ksevelyar/habits-stepper/case/mixin.scad

wall = 2;
overcut = 0.1;
battery_slot_diameter = 32.5;
diameter = 72;
display_length = 77;
display_pcb_width = 19.2;
display_slot_width = 21;
display_slot_length = 67;
display_window_length = 56;
display_window_width = 17.4;
esp32c3_width = 18.5;
esp32c3_length = 24;
tp4057_width = 14.5;
tp4057_length = 14;

module rail_side(half_width, length, y, rail_height = 9) {
  translate([-half_width - 2, y, 2]) cube([2, length, rail_height]);
  hull() {
    translate([-half_width - 0.15, y, 2 + rail_height - 3.5]) rotate([0, -40, 0]) cube([1.5, length, 1]);
    translate([-half_width - 0.5, y, 2 + rail_height - 2.6]) cube([1.5, length, 1]);
  }
  translate([-half_width - 0.35, y, 2 + rail_height - 1.0]) rotate([0, -40, 0]) cube([1.3, length, 1]);
}

module rail(half_width, length, y, rail_height = 9) {
  rail_side(half_width, length, y, rail_height);
  mirror([1, 0, 0]) rail_side(half_width, length, y, rail_height);
}

module esp32c3_mini_rails() {
  rail(esp32c3_width / 2, esp32c3_length - 8, 19);
}

module tp4057_rails() {
  rail(tp4057_width / 2, tp4057_length, -36, 13);
}

module button_cutout() {
  size = 14.1;
  translate([-size / 2, -24.5, -2.5]) cube(size=size);
}

module display_slot_cutout() {
  translate([-display_slot_length / 2, (display_pcb_width - display_slot_width) / 2, 0.4]) cube([display_slot_length, display_slot_width, 100]);
}

module display_window_cutout(clearance = 0) {
  width = display_window_width + clearance;
  translate([-display_window_length / 2, (display_pcb_width - width) / 2, -0.1])
    cube([display_window_length, width, 100]);
}

module display() {
  difference() {
    hull() {
      length = display_length + wall * 2 + 0.5;
      width = display_pcb_width + wall * 2 + 0.5;
      translate([-length / 2, 0, 0]) cube(size=[length, width, height]);

      cylinder(h=height, d=diameter + wall * 2, $fn=256);
    }

    hull() {
      length = display_length + 0.5;
      width = display_pcb_width + 3.5;
      translate([-length / 2, 0, wall]) cube(size=[length, width, height + wall]);

      translate([0, 0, wall]) cylinder(h=height, d=diameter + 0.3, $fn=256);
    }
  }
}

module type_c_cutout() {
  translate([0, diameter / 2 + 4, 8.5]) rotate([90, 0, 0])
      hull() {
        translate([-2.9, 0, 0]) cylinder(h=10, d=3.7, $fn=64);
        translate([2.9, 0, 0]) cylinder(h=10, d=3.7, $fn=64);
      }
}

module leg(leg_height) {
  difference() {
    cylinder(h=leg_height, d=6.24, $fn=32);
    cylinder(h=leg_height + 1, d=3, $fn=32);
  }
}
